MOSH-Insa-Toulouse/2021_2022_LIEVRE_NGUYEN/2_Piste_bleue/screen_ttn_end_device.PNG

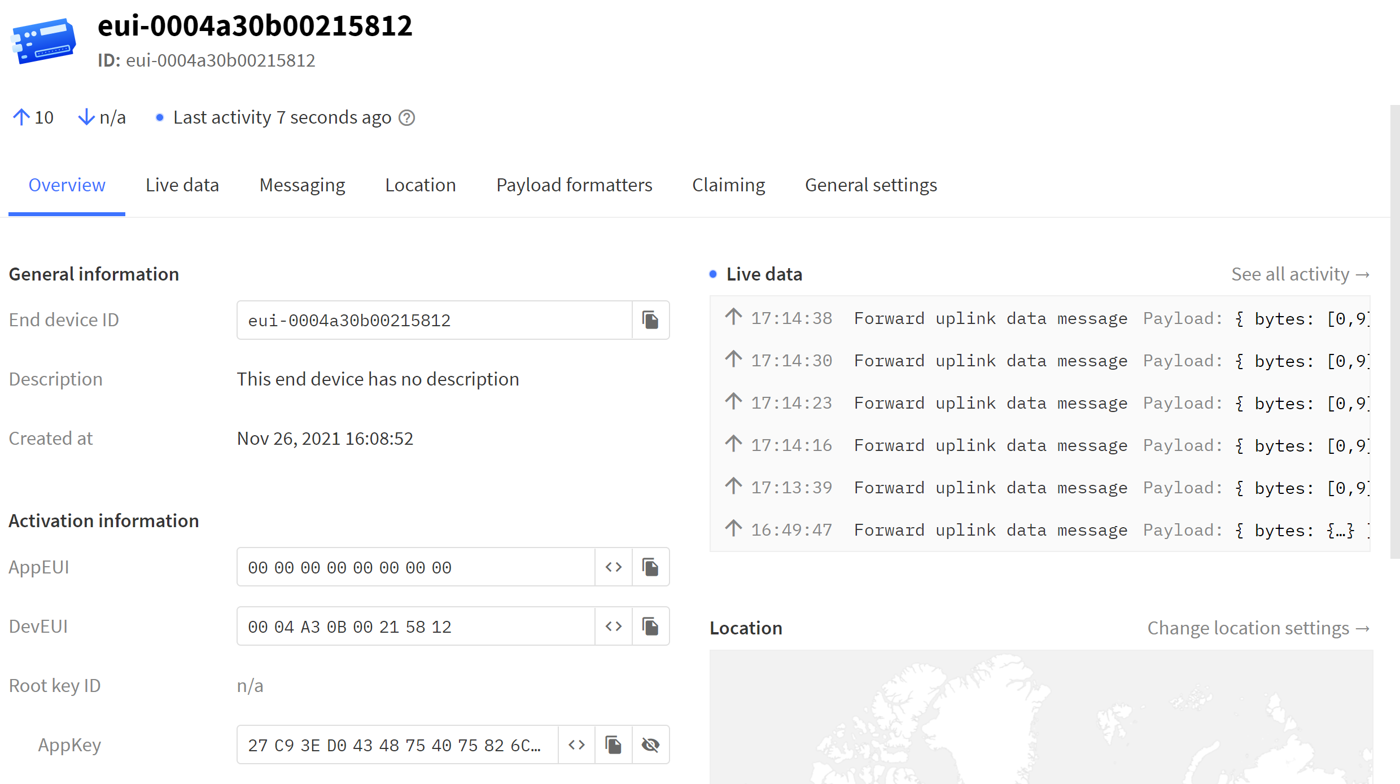
2_Piste_bleue/screen_ttn_end_device.PNG
