MOSH-Insa-Toulouse/2021_2022_LIEVRE_NGUYEN/Documents/Pictures/AIME_GSWO3_1.jpg

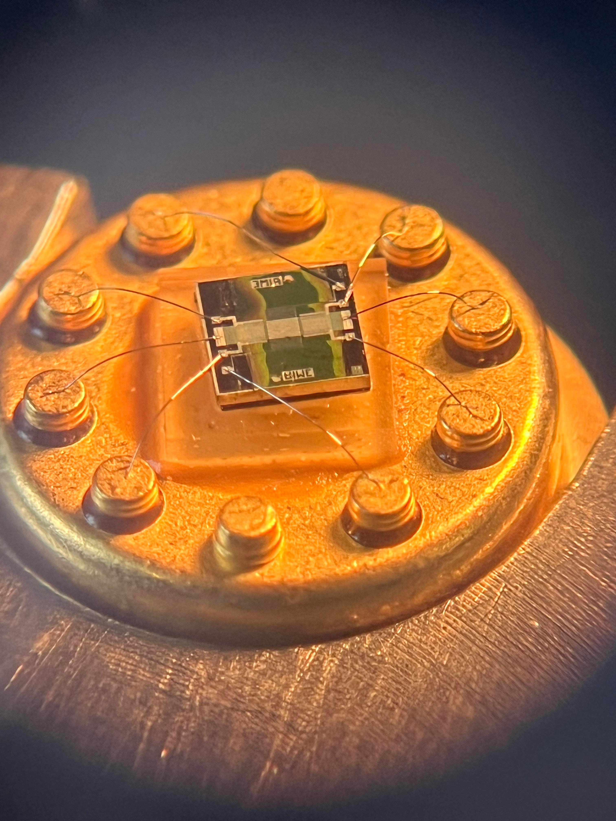
Documents/Pictures/AIME_GSWO3_1.jpg
