MOSH-Insa-Toulouse/2021_2022_LIEVRE_NGUYEN/Documents/Pictures/AIME_GSWO3_4.jpg

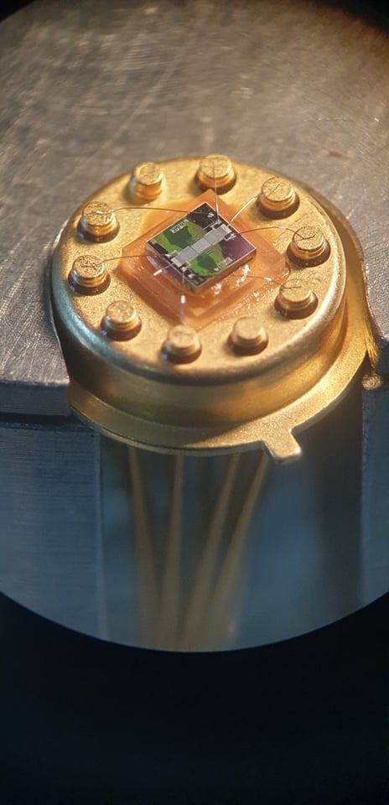
Documents/Pictures/AIME_GSWO3_4.jpg
