MOSH-Insa-Toulouse/2021_2022_LIEVRE_NGUYEN/Documents/Pictures/config_sensor.png

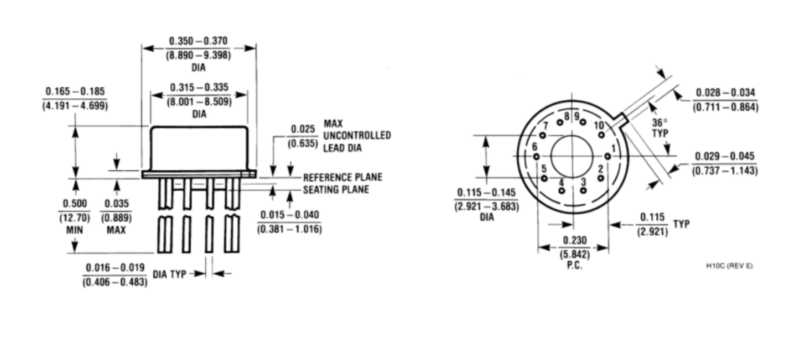
Documents/Pictures/config_sensor.png
