MOSH-Insa-Toulouse/2021_2022_LIEVRE_NGUYEN/Documents/Pictures/NODERED_dashboard.PNG

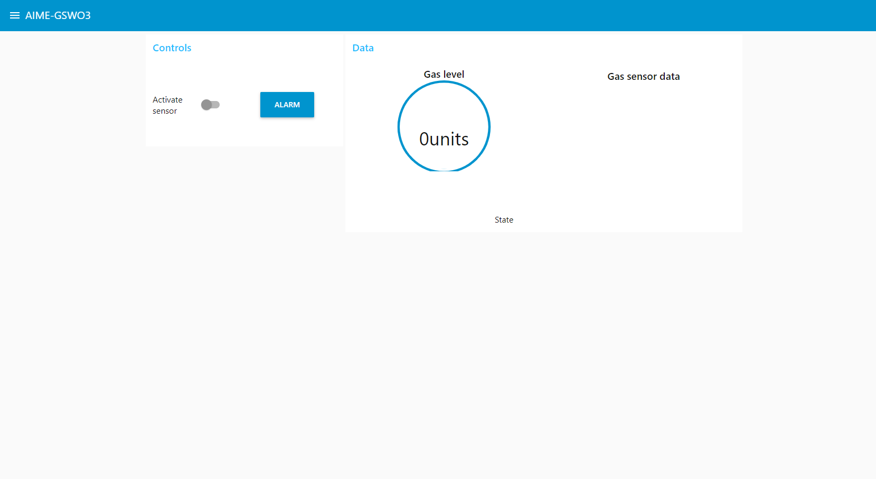
Documents/Pictures/NODERED_dashboard.PNG
